boschsensortec/three-axis-accelerometer-model/X_axis_electrode_short.STL

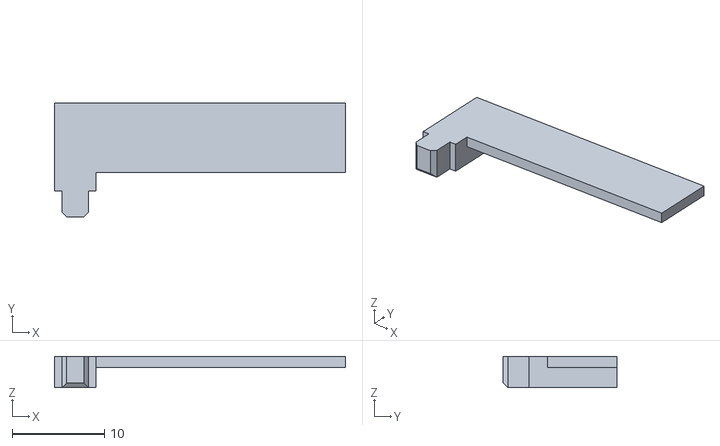
[picture p23: CAD file, 2025-11-06]
X_axis_electrode_short.STL
31.5 x 12.3 x 3.40
